Paul193247/Jugendforscht-Wolfserkennung/tests/Erster Versuch mit Hund/img20241124_051948_1.png

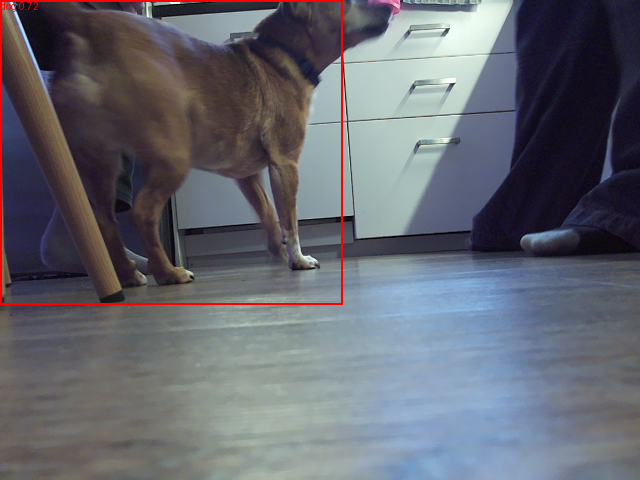
tests/Erster Versuch mit Hund/img20241124_051948_1.png
