Paul193247/Jugendforscht-Wolfserkennung/tests/Erster Versuch mit Katze/img20241116_132913_1.png

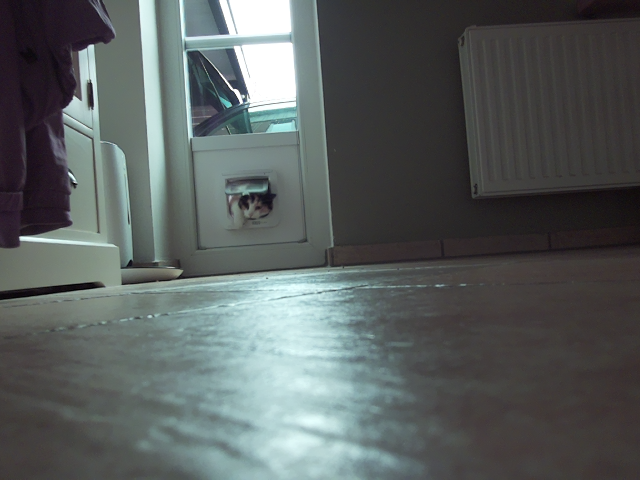
tests/Erster Versuch mit Katze/img20241116_132913_1.png
