Paul193247/Jugendforscht-Wolfserkennung/tests/Erster Versuch mit Katze/img20241116_134552_2.png

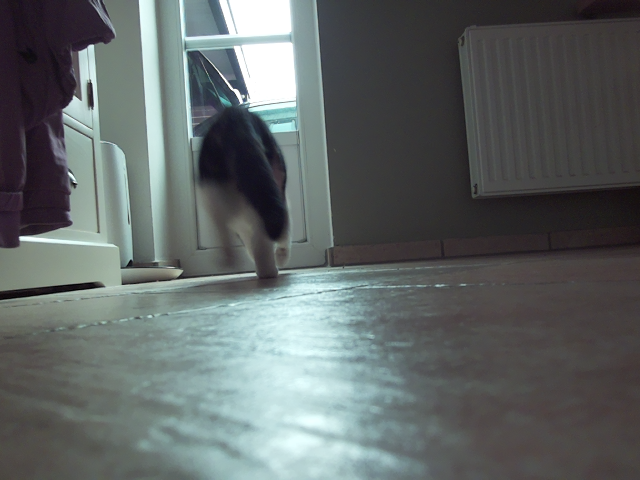
tests/Erster Versuch mit Katze/img20241116_134552_2.png
