Paul193247/Jugendforscht-Wolfserkennung/tests/Zweiter Versuch mit Hund/img20241124_082959_4.png

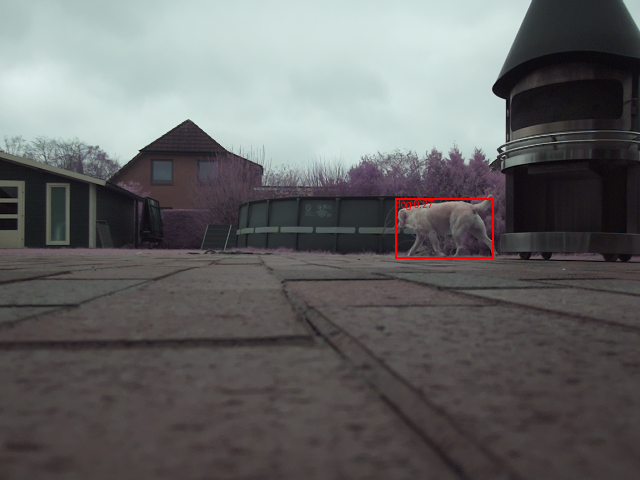
tests/Zweiter Versuch mit Hund/img20241124_082959_4.png
