Paul193247/Jugendforscht-Wolfserkennung/tests/Zweiter Versuch mit Hund/img20241124_083248_1.png

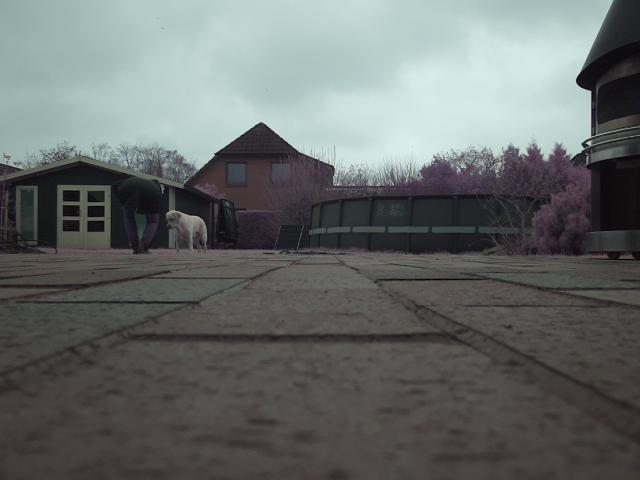
tests/Zweiter Versuch mit Hund/img20241124_083248_1.png
