Paul193247/Jugendforscht-Wolfserkennung/tests/Zweiter Versuch mit Hund/img20241124_083831_3.png

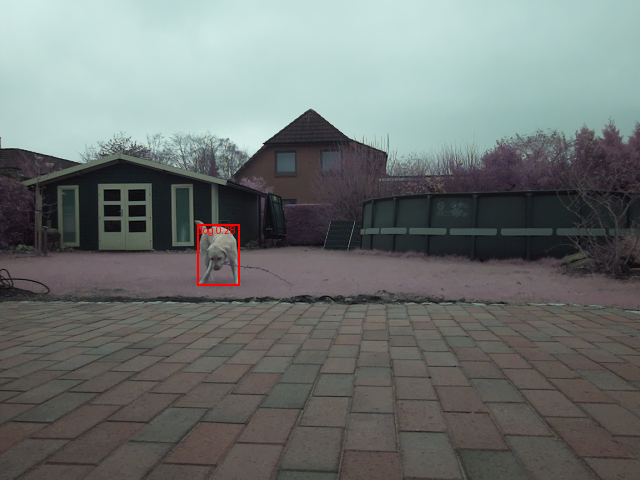
tests/Zweiter Versuch mit Hund/img20241124_083831_3.png
